monica-raluca/OpenBook/Images/Second_Side_OpenBook.png

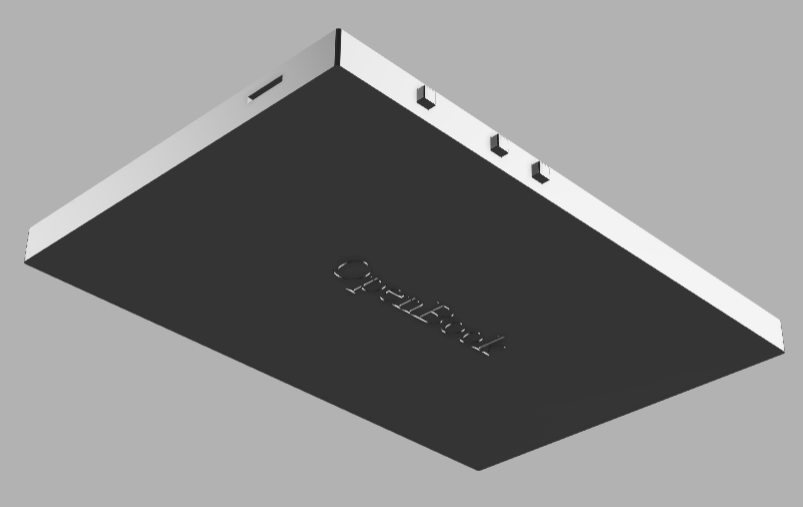
Images/Second_Side_OpenBook.png
